EdwinBontenbal/InterGasGateway/MQTTExplorer/IC2_Burner.JPG

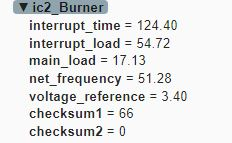
MQTTExplorer/IC2_Burner.JPG
