EdwinBontenbal/InterGasGateway/MQTTExplorer/IC2_Code.JPG

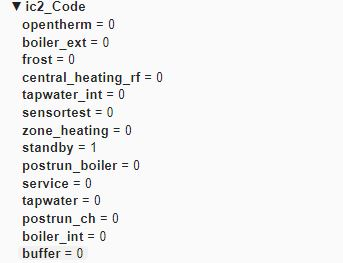
MQTTExplorer/IC2_Code.JPG
