EdwinBontenbal/InterGasGateway/MQTTExplorer/IC2_Faults.JPG

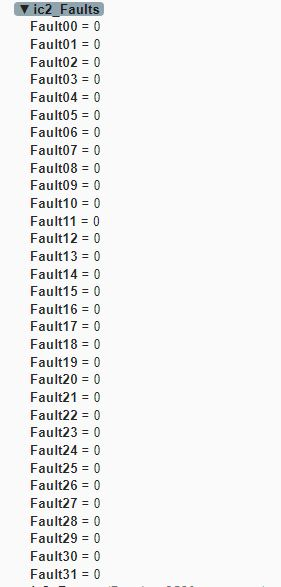
MQTTExplorer/IC2_Faults.JPG
