EdwinBontenbal/InterGasGateway/MQTTExplorer/IC2_Parameters.JPG

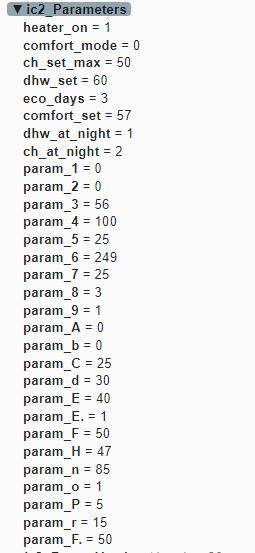
MQTTExplorer/IC2_Parameters.JPG
