EdwinBontenbal/InterGasGateway/MQTTExplorer/IC2_Status.JPG

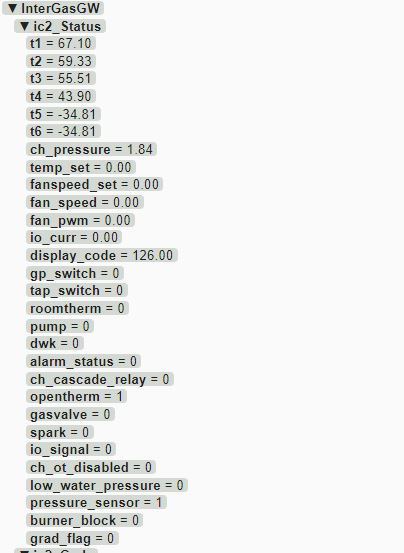
MQTTExplorer/IC2_Status.JPG
