EdwinBontenbal/InterGasGateway/Pictures/DrillHoles_PCB.png

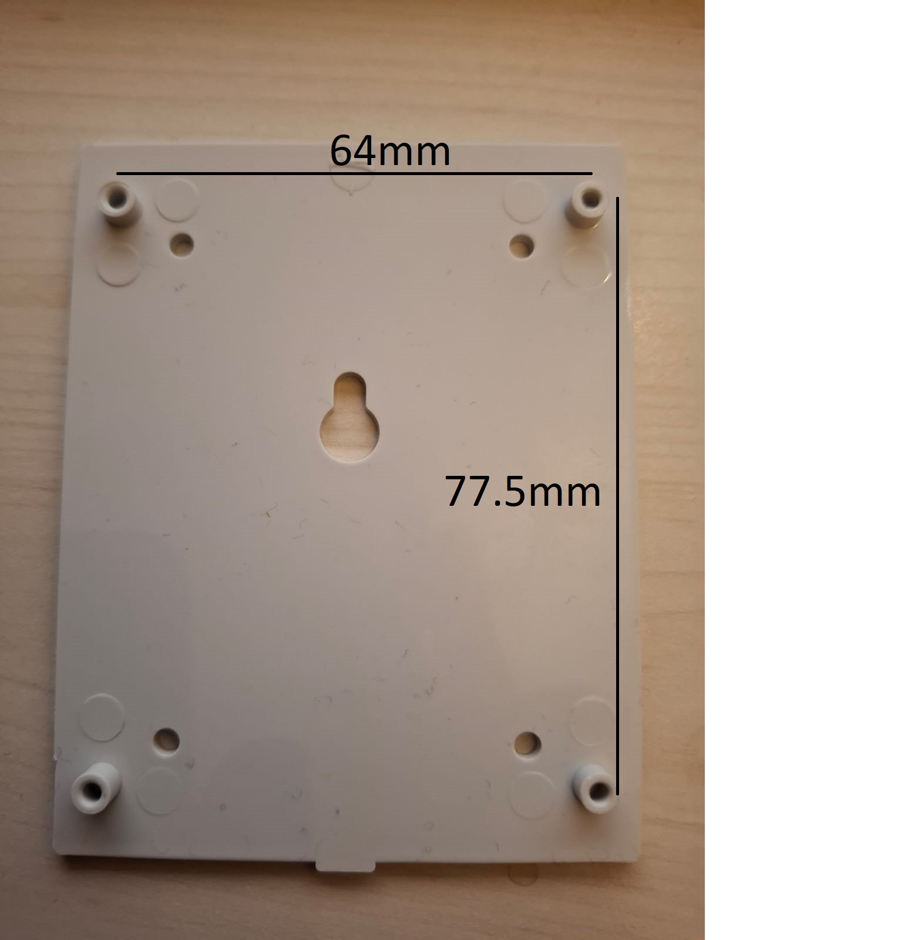
Pictures/DrillHoles_PCB.png
