EdwinBontenbal/InterGasGateway/Pictures/Molex 5557 4pin.PNG

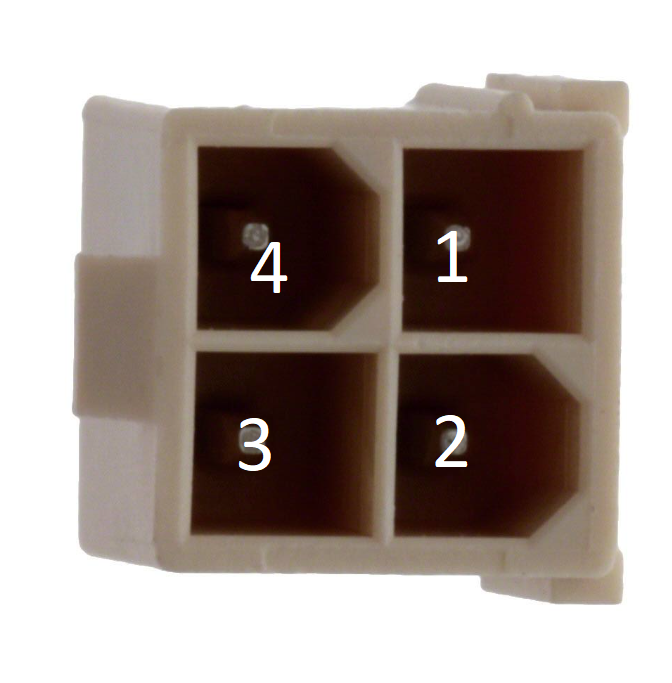
Pictures/Molex 5557 4pin.PNG
