EdwinBontenbal/InterGasGateway/MQTTExplorer/IC2_OperatingHours.JPG

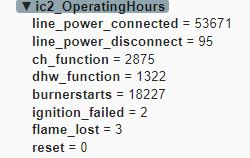
MQTTExplorer/IC2_OperatingHours.JPG
