EdwinBontenbal/InterGasGateway/Test/TestSetup.jpg

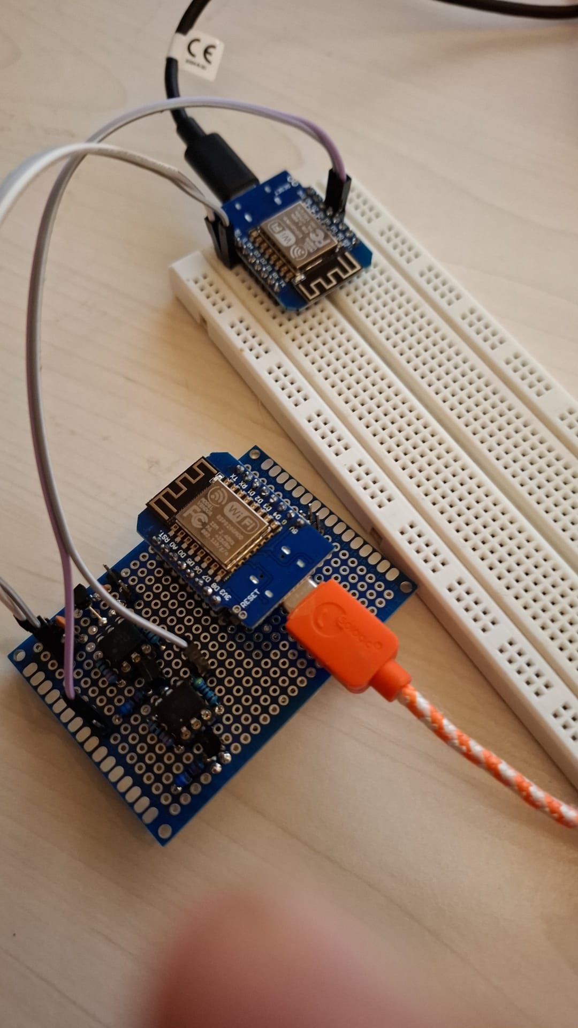
Test/TestSetup.jpg
