EdwinBontenbal/InterGasGateway/ArduinoCode/WithStateMachine/EnvironmentSettings.h

// Define Wifi for esp8266 settings
const char*     ssid          = "XXX";				// Put your SSID here
const char*     password      = "XXX";				// Put our Wifi password here
const char*     hostname      = "InterGas GW";
//
// Define mqtt settings
const char*     mqtt_server   = "XX";				// Put your MQTT IP adress here
const int       mqtt_port     = 1883;				// Put your MQTT port      here
const char*     mqtt_user     = "";
const char*     mqtt_password = "";
const char*     Gl_Topic1     = "InterGasGW";
